HMS-RIC/CageWheel/Photos/_1160658.JPG

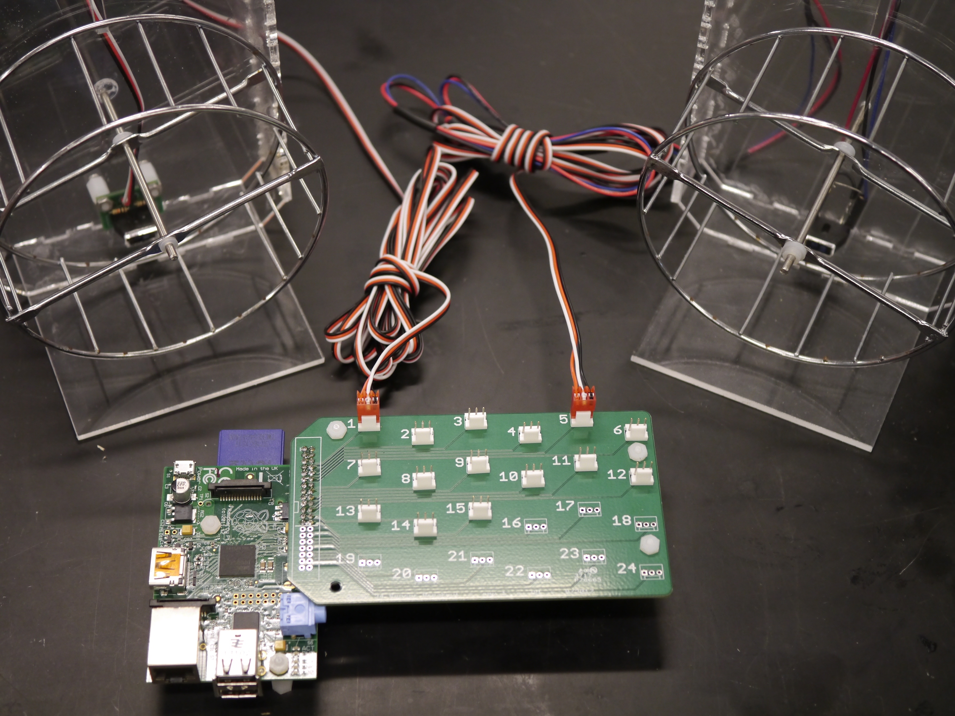
Photos/_1160658.JPG
