HMS-RIC/CageWheel/Photos/_1160659.JPG

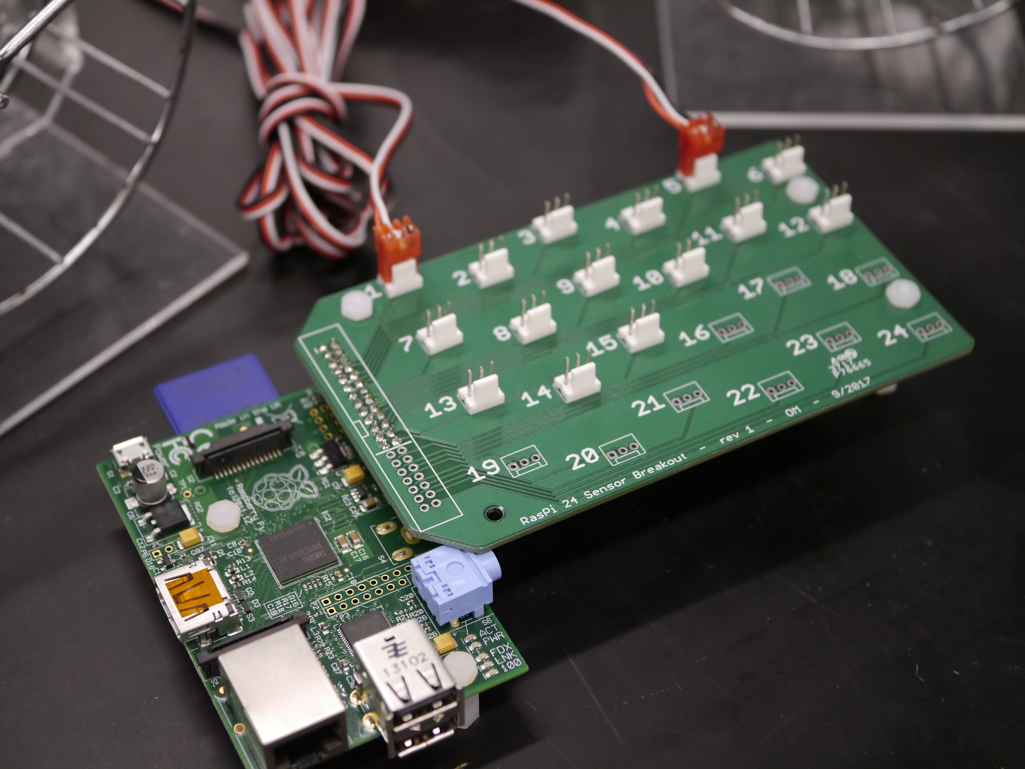
Photos/_1160659.JPG
