HMS-RIC/CageWheel/Photos/_1160660.JPG

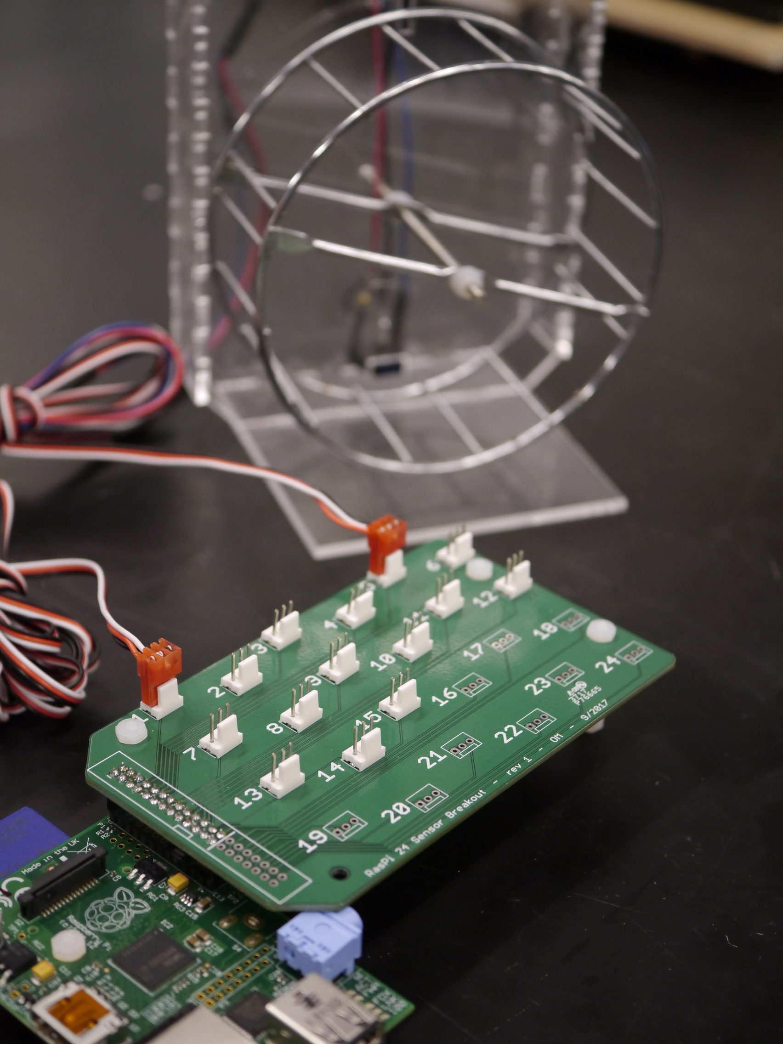
Photos/_1160660.JPG
