HMS-RIC/CageWheel/Photos/_1160662.JPG

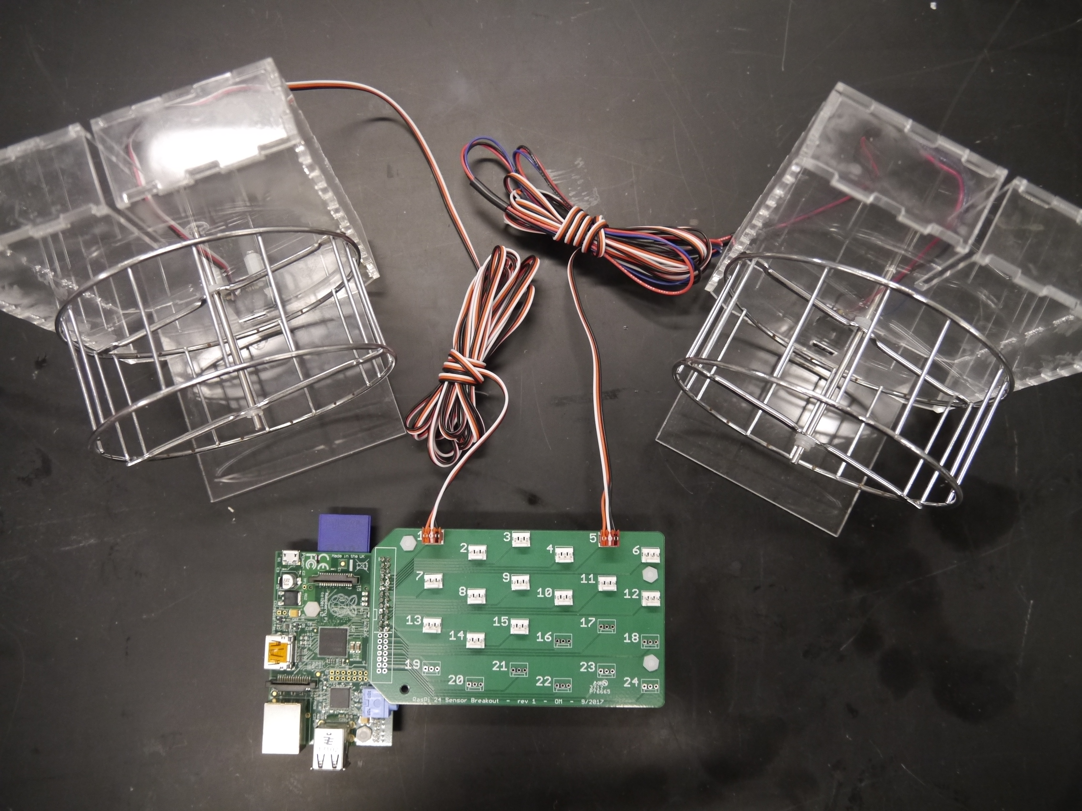
Photos/_1160662.JPG
