HMS-RIC/CageWheel/Photos/_1160663.JPG

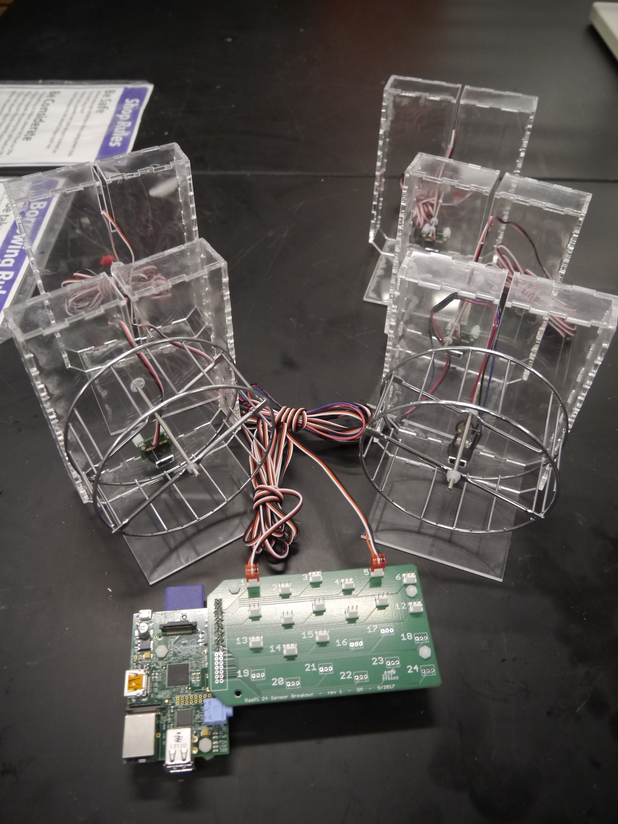
Photos/_1160663.JPG
