HMS-RIC/CageWheel/Photos/_1160664.JPG

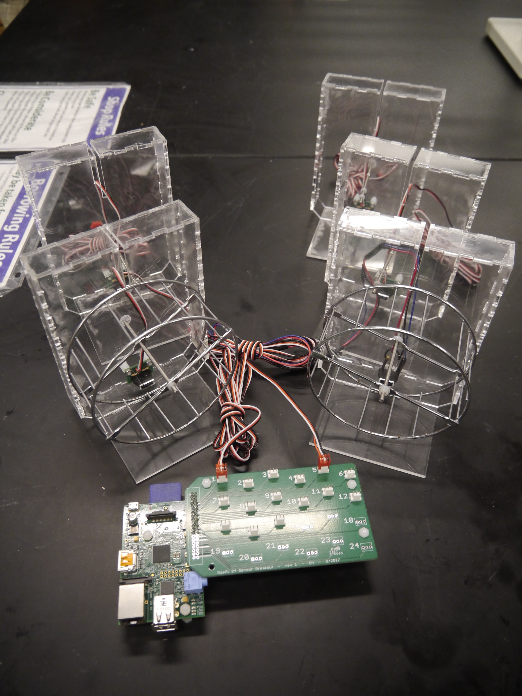
Photos/_1160664.JPG
