HMS-RIC/CageWheel/Photos/_1160677.JPG

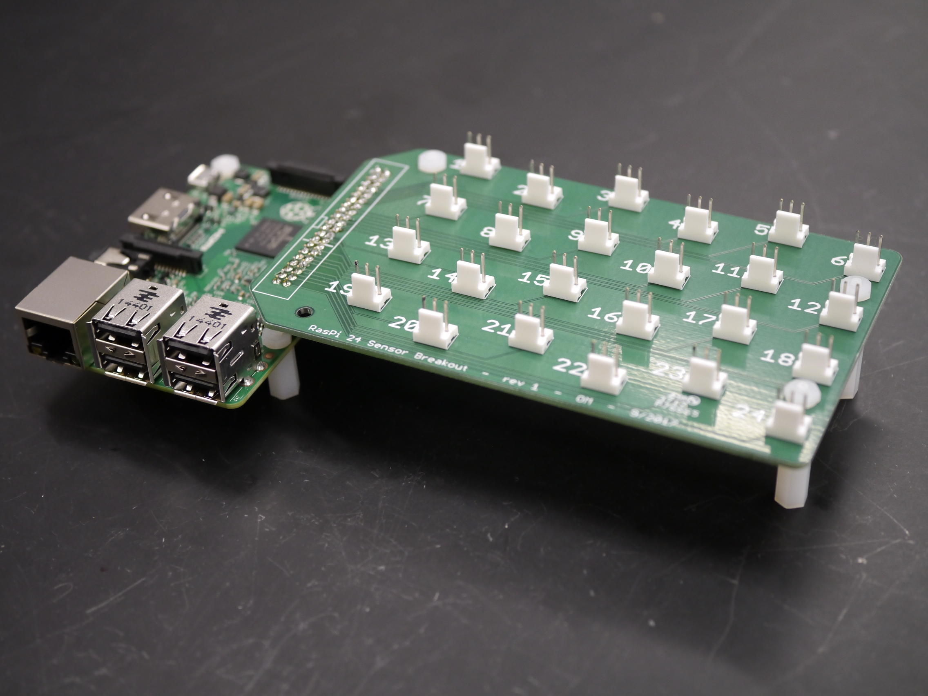
Photos/_1160677.JPG
