HMS-RIC/CageWheel/Photos/_1160678.JPG

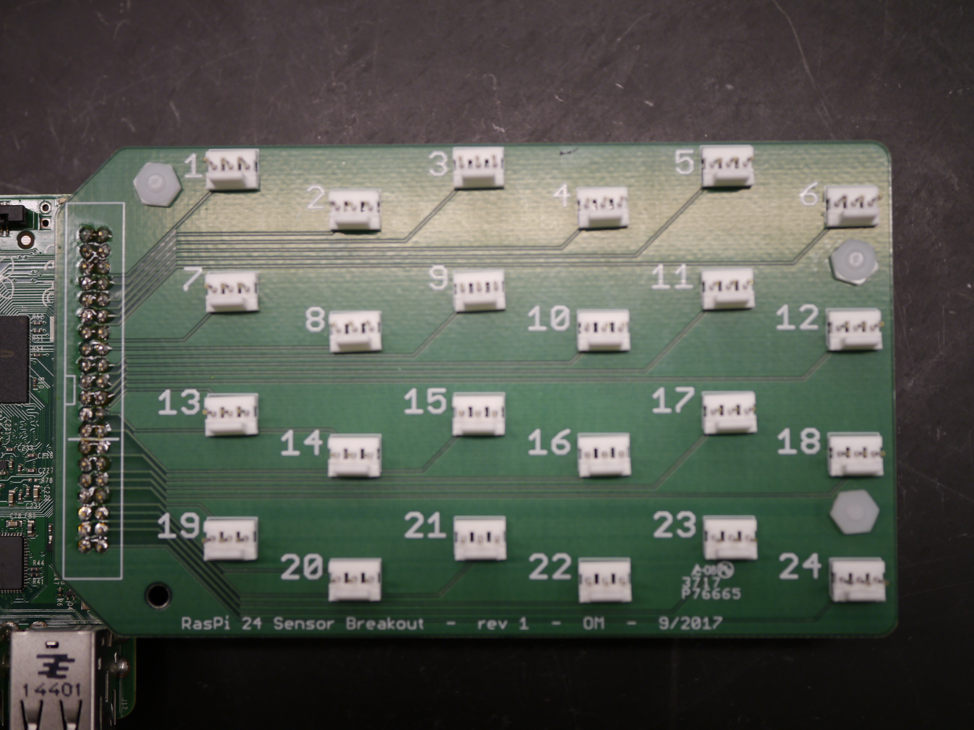
Photos/_1160678.JPG
