HMS-RIC/CageWheel/Photos/_1160679.JPG

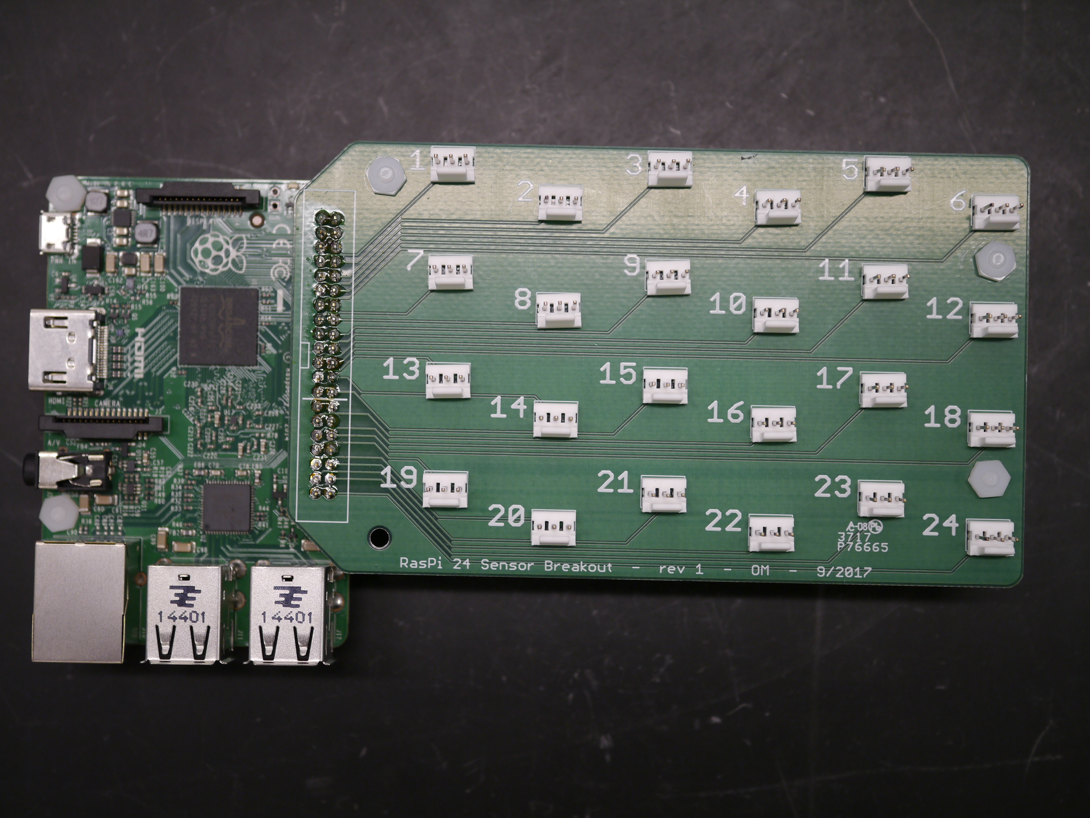
Photos/_1160679.JPG
