HMS-RIC/CageWheel/Photos/_1160680.JPG

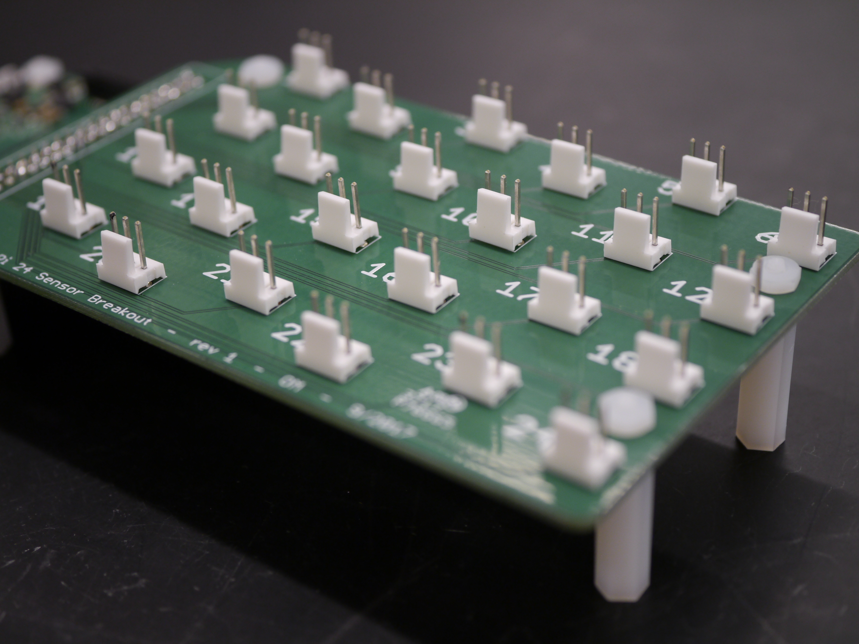
Photos/_1160680.JPG
