HMS-RIC/CageWheel/Photos/_1160681.JPG

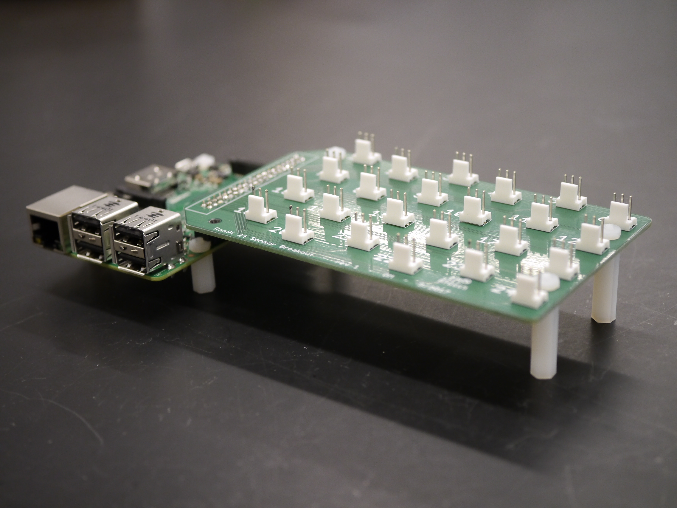
Photos/_1160681.JPG
