HMS-RIC/CageWheel/Photos/_1160682.JPG

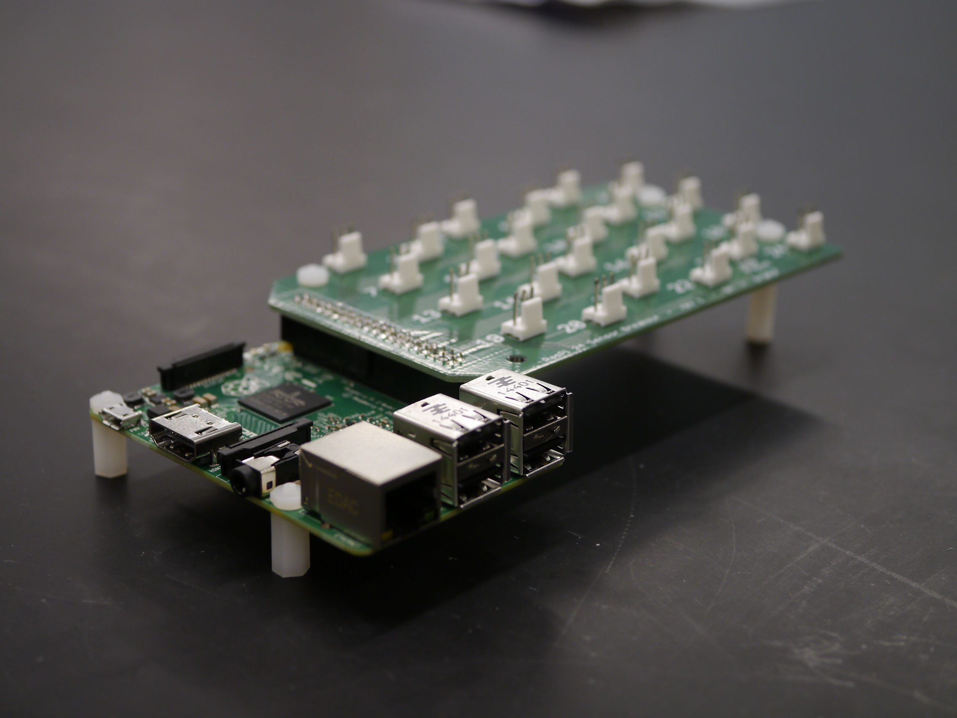
Photos/_1160682.JPG
