HMS-RIC/CageWheel/Photos/_1160683.JPG

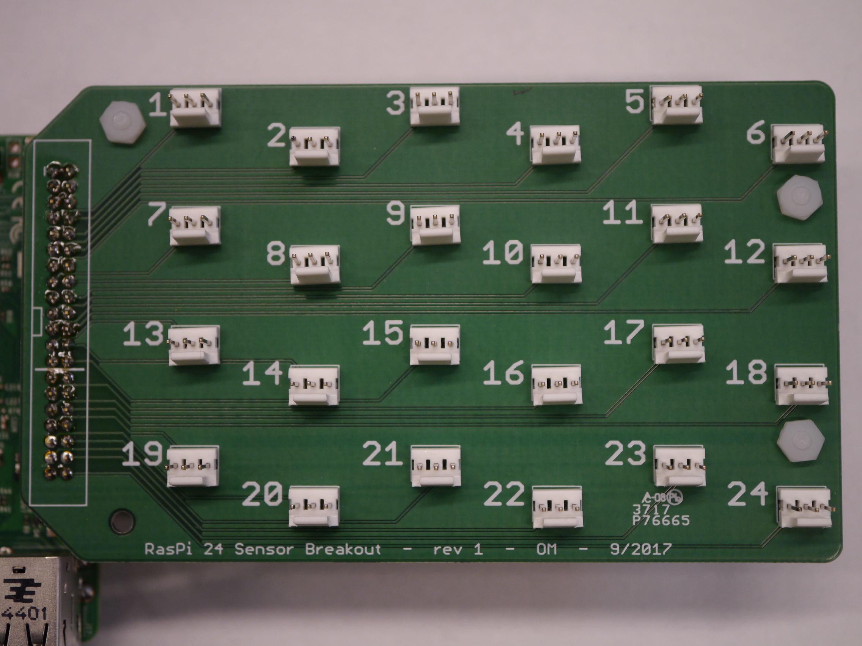
Photos/_1160683.JPG
