HMS-RIC/CageWheel/Photos/_1160684.JPG

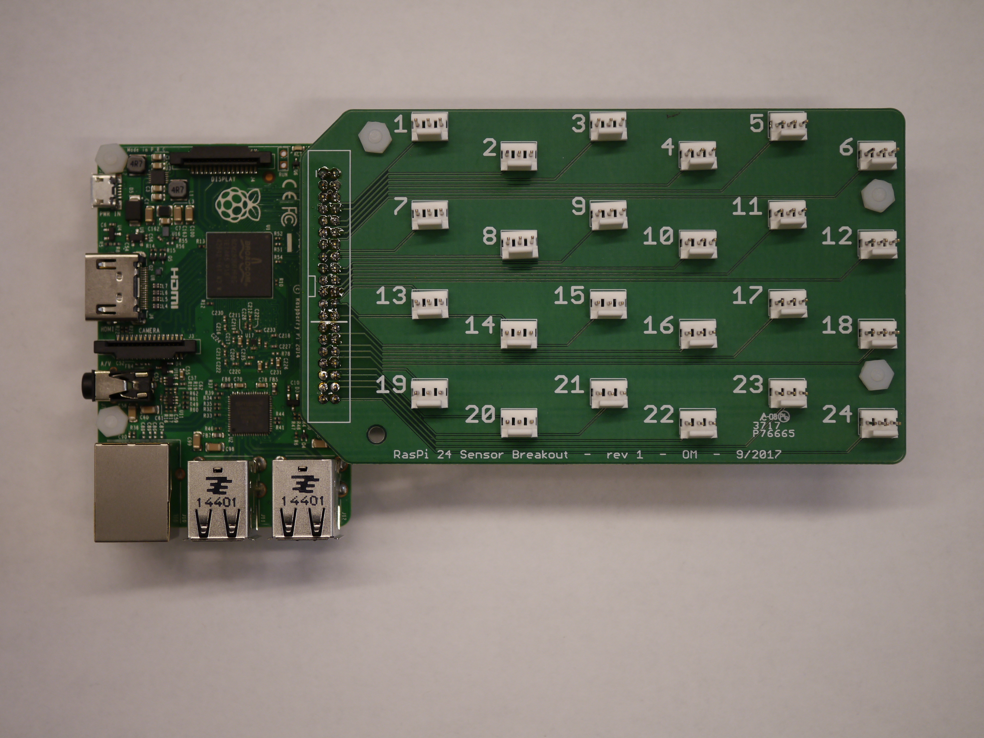
Photos/_1160684.JPG
