HMS-RIC/CageWheel/Photos/_1160686.JPG

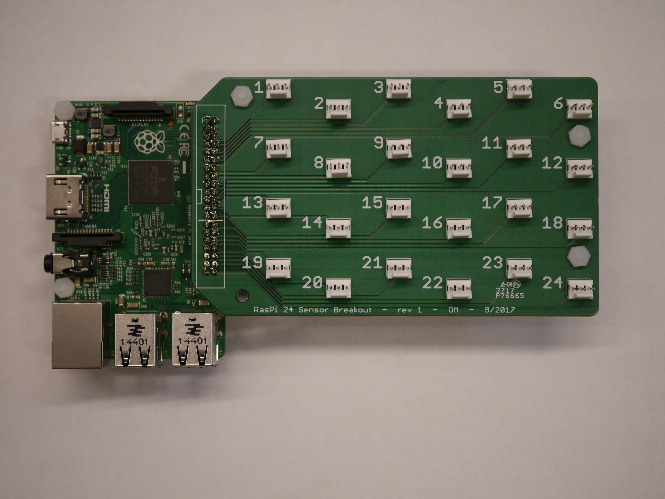
Photos/_1160686.JPG
