HMS-RIC/CageWheel/Photos/IMG_0312.JPG

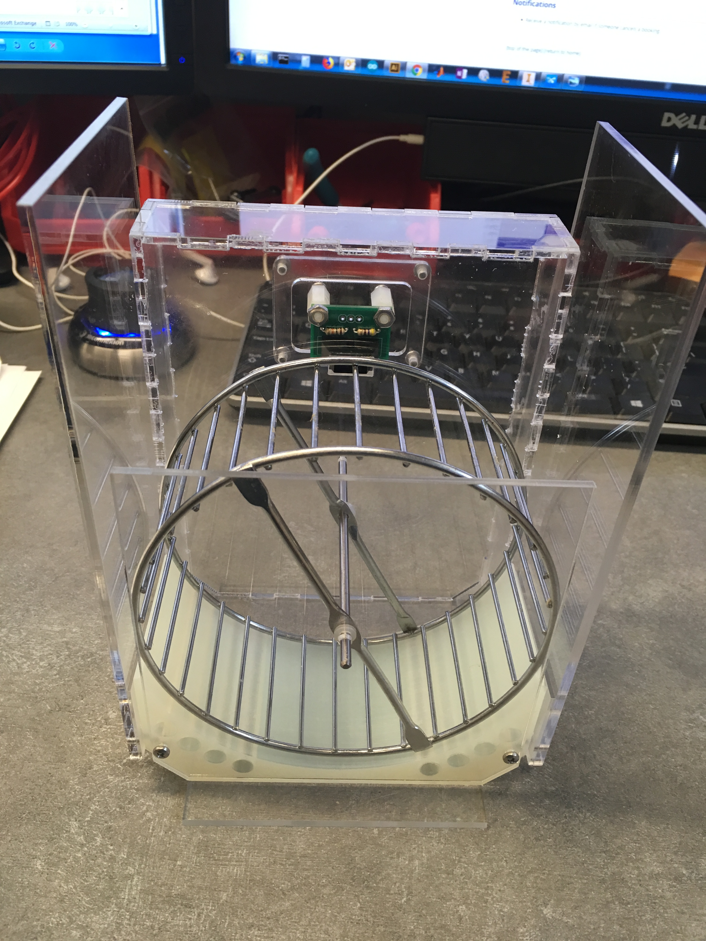
Photos/IMG_0312.JPG
