HMS-RIC/CageWheel/Photos/IMG_0313.JPG

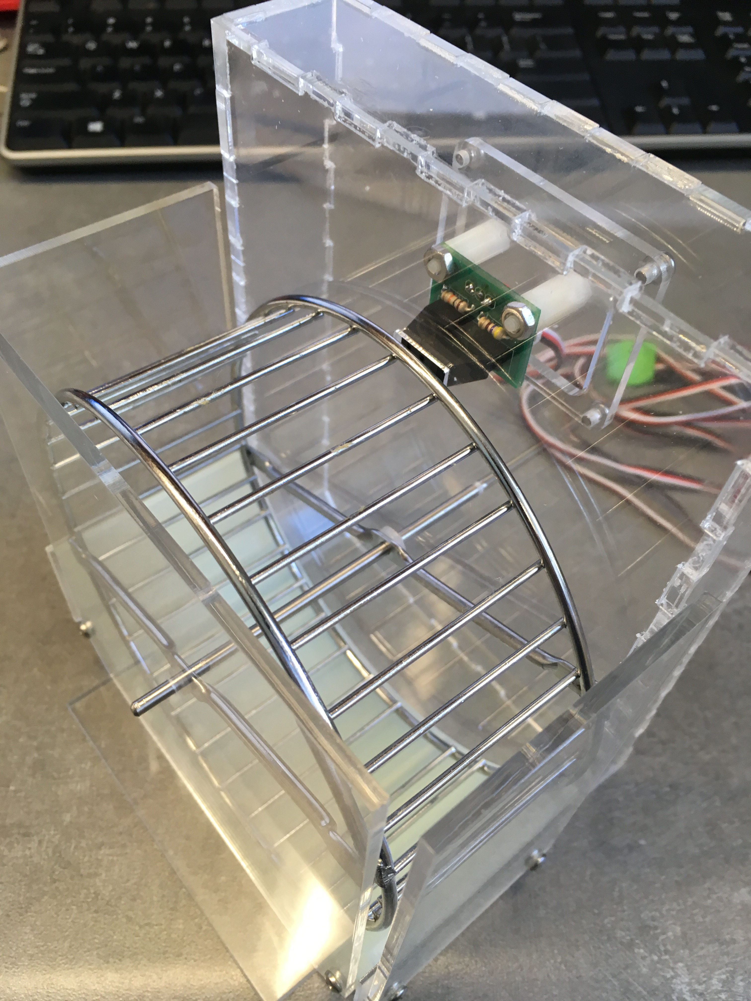
Photos/IMG_0313.JPG
