HMS-RIC/CageWheel/Photos/IMG_0314.JPG

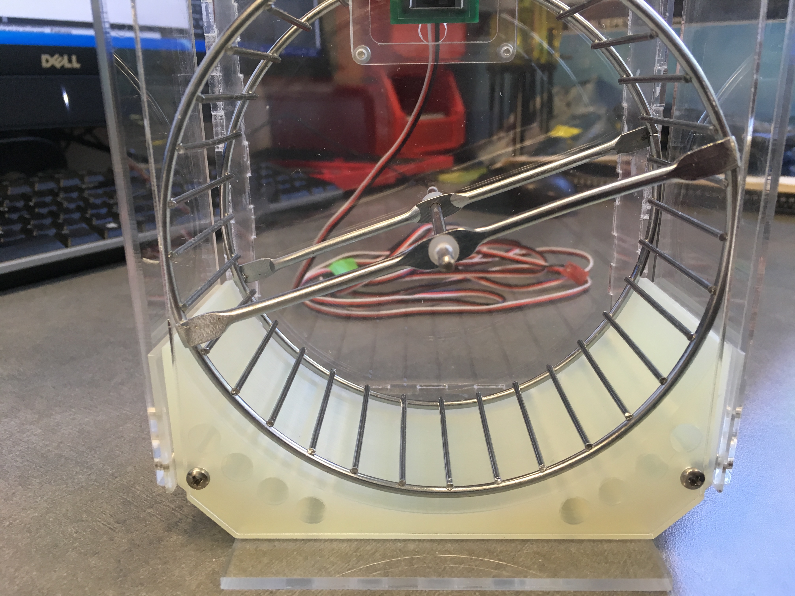
Photos/IMG_0314.JPG
