HMS-RIC/CageWheel/Photos/IMG_0492.JPG

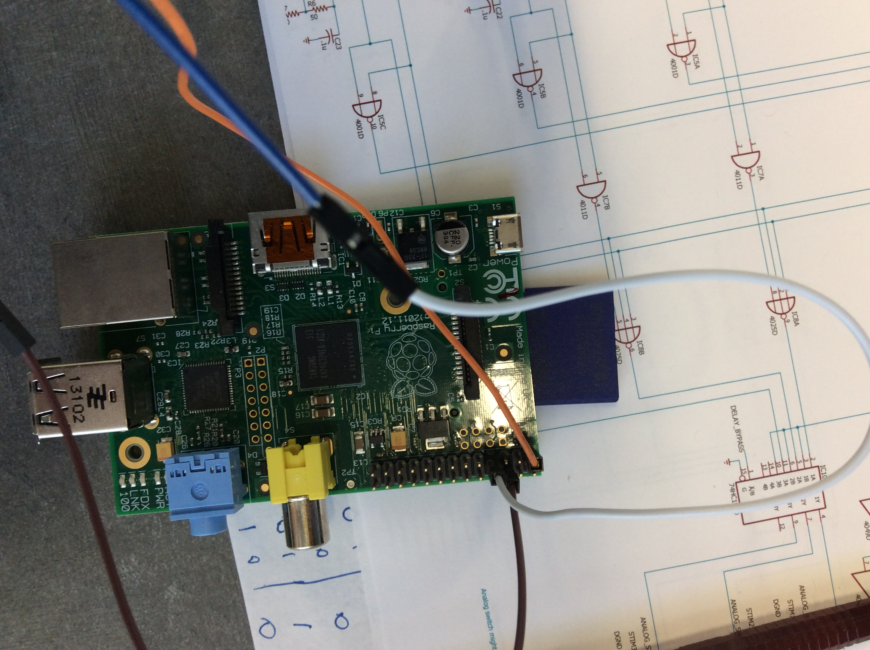
Photos/IMG_0492.JPG
