HMS-RIC/CageWheel/Photos/IMG_0493.JPG

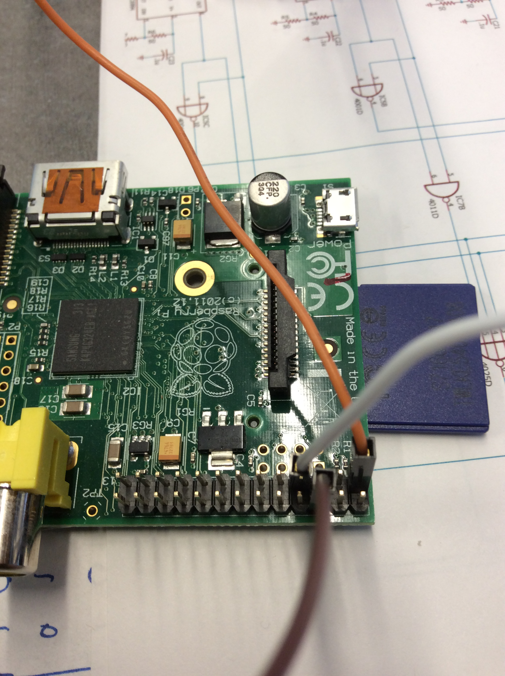
Photos/IMG_0493.JPG
