HMS-RIC/CageWheel/Photos/IMG_0494.JPG

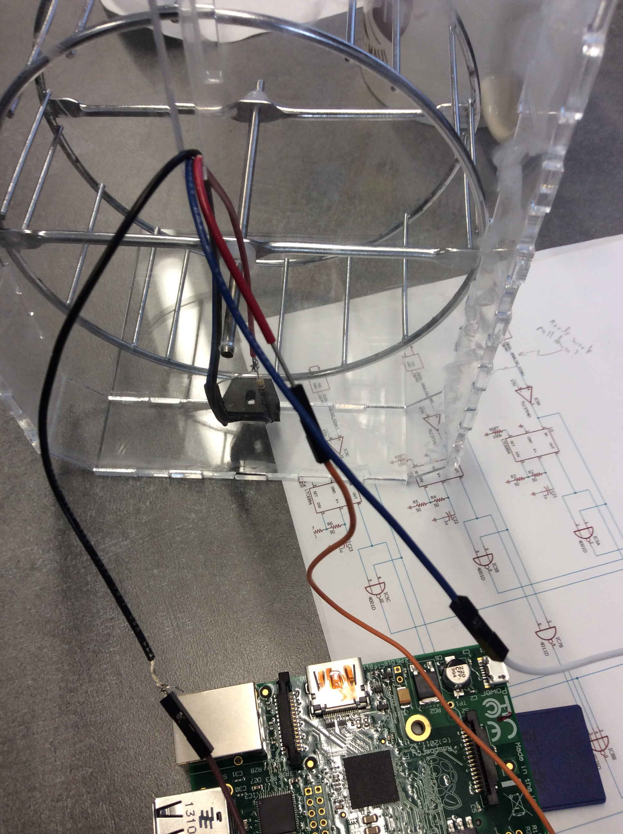
Photos/IMG_0494.JPG
