HMS-RIC/CageWheel/Photos/IMG_3197.JPG

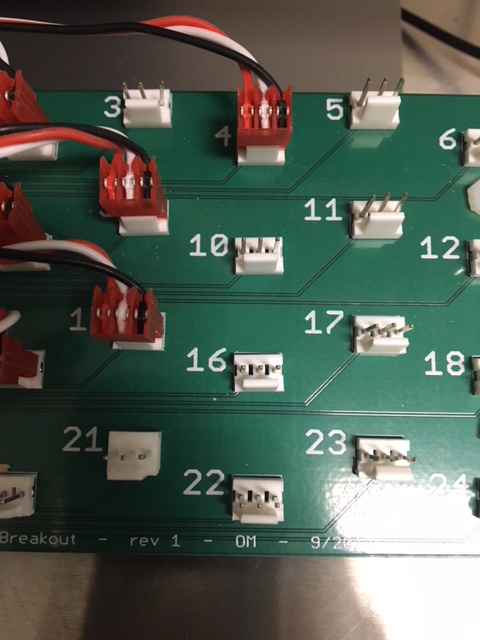
Photos/IMG_3197.JPG
